Shizuku-g/BV002/BV002/pcb/BV002REV1.5/3d/XT30PW-M.stp

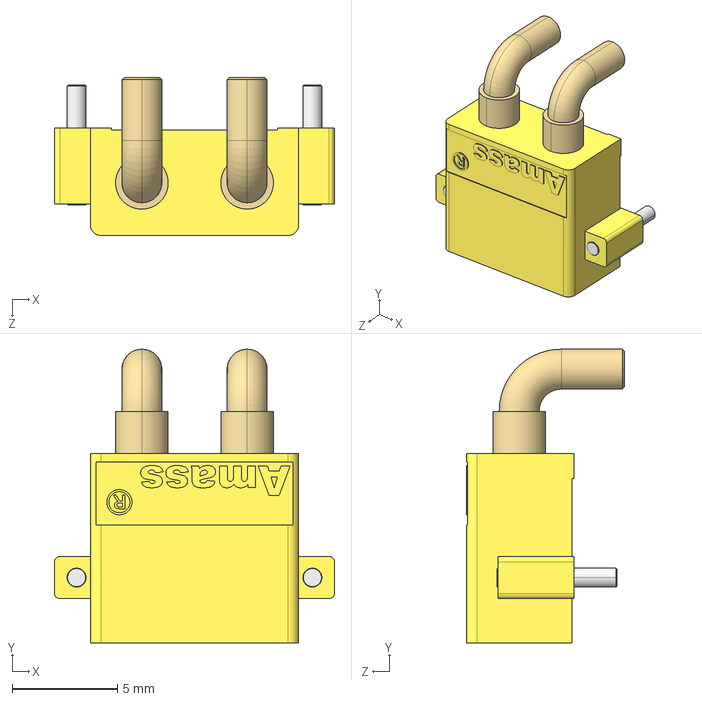
[picture p18: CAD file, 2026-07-18]
BV002/pcb/BV002REV1.5/3d/XT30PW-M.stp
13.3 x 13.9 x 7.50 mm
