Shizuku-g/BV002/BV002/pcb/BV002REV1.5/3d/SLC1175-271MEC_COC.step

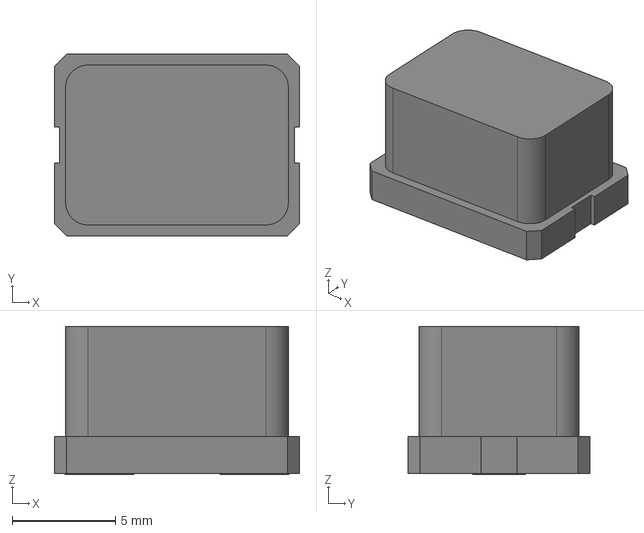
[picture p19: CAD file, 2026-07-18]
BV002/pcb/BV002REV1.5/3d/SLC1175-271MEC_COC.step
11.9 x 8.83 x 7.19 mm
