Shizuku-g/BV002/BV002/pcb/BV002REV1.5/3d/heatsink-13x12x5.step

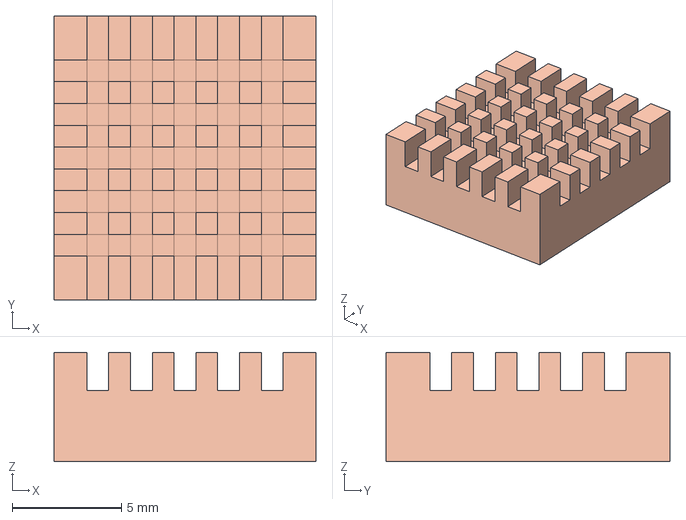
[picture p20: CAD file, 2026-07-18]
BV002/pcb/BV002REV1.5/3d/heatsink-13x12x5.step
12.0 x 13.0 x 5.00 mm
