Shizuku-g/BV002/BV002/pcb/BV002REV1.5/3d/SIS0011A.stp

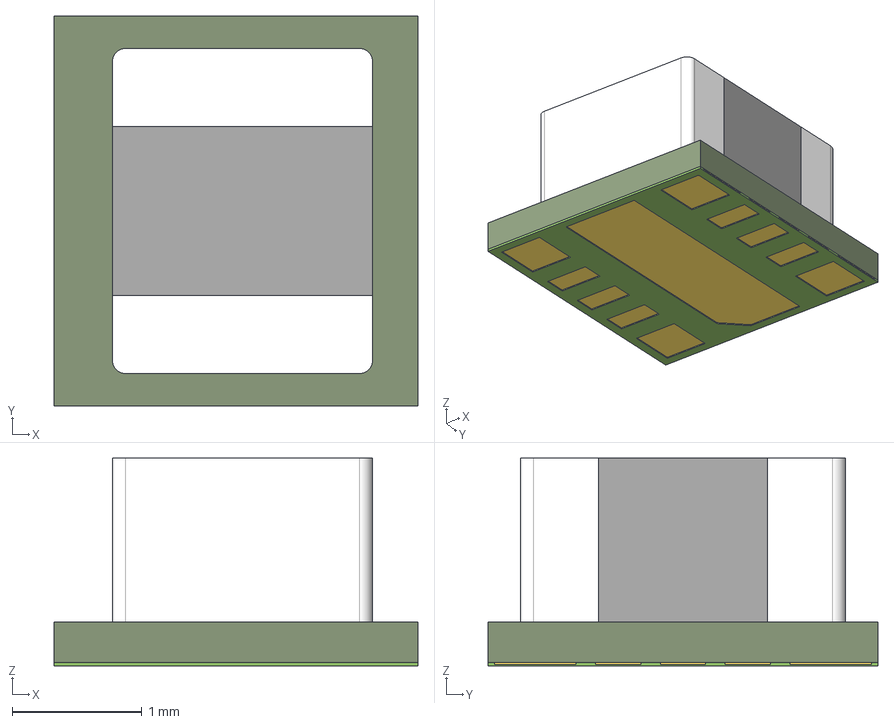
[picture p21: CAD file, 2026-07-18]
BV002/pcb/BV002REV1.5/3d/SIS0011A.stp
2.80 x 3.00 x 1.60 mm
SOLDERMASK-SIS0011A
METAL-SIS0011A
SUBSTRATE-SIP
INDUCTOR-BODY-MLV
INDUCTOR-TERMNL-MLV x 2
