Shizuku-g/BV002/BV002/pcb/BV002REV1.5/3d/IND_VLS6045EX-4R7M_TDK.stl

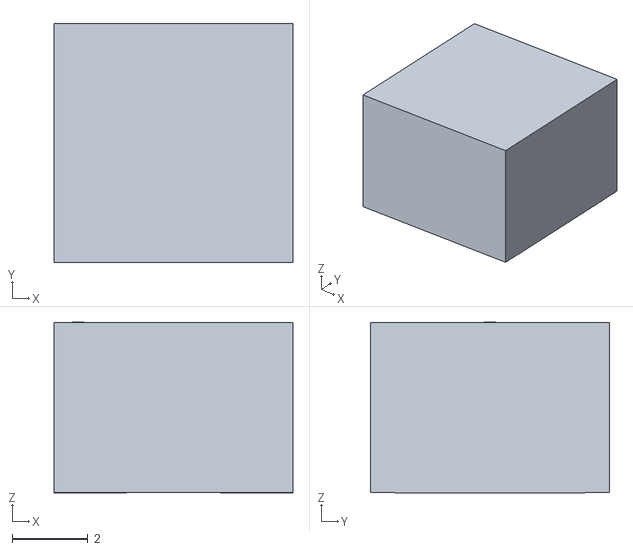
[picture p22: CAD file, 2026-07-18]
BV002/pcb/BV002REV1.5/3d/IND_VLS6045EX-4R7M_TDK.stl
6.30 x 6.30 x 4.50
